quarkcz/watermeter_esp32/src/ikony.h

#pragma once
#include <Arduino.h>
#include <Adafruit_SSD1306.h>

//
// === Deklarace ikon jako bitmap ===
//

// ⚠️ Ikona DANGER 24×24 px
const unsigned char icon_danger24x24[] PROGMEM = {
    0x00,0x00,0x00,  // ........................
    0x00,0x00,0x00,  // ........................
    0x00,0x00,0x00,  // ........................
    0x00,0x18,0x00,  // ...........##...........
    0x00,0x3C,0x00,  // ..........####..........
    0x00,0x7E,0x00,  // .........######.........
    0x00,0x66,0x00,  // .........##..##.........
    0x00,0xE7,0x00,  // ........###..###........
    0x00,0xC3,0x00,  // ........##....##........
    0x01,0x99,0x80,  // .......##..##..##.......
    0x03,0x99,0xC0,  // ......###..##..###......
    0x03,0x18,0xC0,  // ......##...##...##......
    0x07,0x18,0xE0,  // .....###...##...###.....
    0x06,0x18,0x60,  // .....##....##....##.....
    0x0C,0x00,0x30,  // ....##............##....
    0x1C,0x18,0x38,  // ...###.....##.....###...
    0x18,0x18,0x18,  // ...##......##......##...
    0x38,0x00,0x1C,  // ..###..............###..
    0x30,0x00,0x0C,  // ..##................##..
    0x3F,0xFF,0xFC,  // ..####################..
    0x1F,0xFF,0xF8,  // ...##################...
    0x00,0x00,0x00,  // ........................
    0x00,0x00,0x00,  // ........................
    0x00,0x00,0x00   // ........................
};

const unsigned char icon_wifi16x16[] PROGMEM = {
    0x00,0x00,  // ................
    0x07,0xE0,  // .....######.....
    0x1F,0xF8,  // ...##########...
    0x7C,0x3E,  // .#####....#####.
    0xF0,0x0F,  // ####........####
    0xE0,0x03,  // ###...........##
    0x07,0xE0,  // .....######.....
    0x1F,0xF8,  // ...##########...
    0x1C,0x38,  // ...###....###...
    0x18,0x08,  // ...##.......#...
    0x01,0x80,  // .......##.......
    0x03,0xC0,  // ......####......
    0x03,0xC0,  // ......####......
    0x03,0xC0,  // ......####......
    0x01,0x80,  // .......##.......
    0x00,0x00   // ................
};

const unsigned char icon_wifi8x7[] PROGMEM = {
    0x18,  // ...##...
    0x7E,  // .######.
    0xC3,  // ##....##
    0x3C,  // ..####..
    0x66,  // .##..##.
    0x18,  // ...##...
    0x18,  // ...##...
};

const unsigned char icon_wifi_no_signal24x24[] PROGMEM = {
    0x00,0x00,0x00,  // ........................
    0x00,0x00,0x00,  // ........................
    0x00,0x00,0x00,  // ........................
    0x00,0x00,0x00,  // ........................
    0x00,0x78,0x8C,  // .........####...#...##..
    0x03,0xFD,0xDC,  // ......########.###.###..
    0x0F,0xC0,0xF8,  // ....######......#####...
    0x1E,0x00,0x78,  // ...####..........####...
    0x38,0x00,0xF8,  // ..###...........#####...
    0x70,0xFD,0xDC,  // .###....######.###.###..
    0x03,0xF8,0x8C,  // ......#######...#...##..
    0x07,0x80,0x00,  // .....####...............
    0x0E,0x00,0x00,  // ....###.................
    0x00,0x3C,0x00,  // ..........####..........
    0x00,0xFF,0x00,  // ........########........
    0x00,0xE7,0x00,  // ........###..###........
    0x00,0x81,0x00,  // ........#......#........
    0x00,0x18,0x00,  // ...........##...........
    0x00,0x18,0x00,  // ...........##...........
    0x00,0x18,0x00,  // ...........##...........
    0x00,0x00,0x00,  // ........................
    0x00,0x00,0x00,  // ........................
    0x00,0x00,0x00,  // ........................
    0x00,0x00,0x00   // ........................
};

const unsigned char icon_water_drop24x24[] PROGMEM = {
    0x00,0x00,0x00,  // ........................
    0x00,0x18,0x00,  // ...........##...........
    0x00,0x3C,0x00,  // ..........####..........
    0x00,0x7E,0x00,  // .........######.........
    0x00,0xE7,0x00,  // ........###..###........
    0x01,0xC3,0x80,  // .......###....###.......
    0x03,0x81,0xC0,  // ......###......###......
    0x03,0x00,0xC0,  // ......##........##......
    0x07,0x00,0xE0,  // .....###........###.....
    0x06,0x00,0x60,  // .....##..........##.....
    0x0E,0x00,0x70,  // ....###..........###....
    0x0C,0x00,0x30,  // ....##............##....
    0x0C,0x00,0x30,  // ....##............##....
    0x0C,0x01,0xB0,  // ....##.........##.##....
    0x0C,0x01,0xB0,  // ....##.........##.##....
    0x0C,0x03,0xB0,  // ....##........###.##....
    0x0E,0x07,0x70,  // ....###......###.###....
    0x06,0x0E,0x60,  // .....##.....###..##.....
    0x07,0x04,0xE0,  // .....###.....#..###.....
    0x03,0xC3,0xC0,  // ......####....####......
    0x01,0xFF,0x80,  // .......##########.......
    0x00,0x7E,0x00,  // .........######.........
    0x00,0x00,0x00,  // ........................
    0x00,0x00,0x00   // ........................
};

const unsigned char icon_water_drop16x16[] PROGMEM = {
    0x00,0x00,  // ................
    0x01,0x80,  // .......##.......
    0x03,0xC0,  // ......####......
    0x06,0x60,  // .....##..##.....
    0x0C,0x30,  // ....##....##....
    0x08,0x10,  // ....#......#....
    0x18,0x18,  // ...##......##...
    0x10,0x08,  // ...#........#...
    0x10,0x28,  // ...#......#.#...
    0x10,0x28,  // ...#......#.#...
    0x10,0x68,  // ...#.....##.#...
    0x18,0xD8,  // ...##...##.##...
    0x0C,0x30,  // ....##....##....
    0x07,0xE0,  // .....######.....
    0x01,0x80,  // .......##.......
    0x00,0x00   // ................
};

const unsigned char icon_lock_1_8x7[] PROGMEM = {
    0x18,  // ...##...
    0x3C,  // ..####..
    0x24,  // ..#..#..
    0x7E,  // .######.
    0x42,  // .#....#.
    0x42,  // .#....#.
    0x7E   // .######.
};

const unsigned char icon_lock_2_8x7[] PROGMEM = {
    0x18,  // ...##...
    0x24,  // ..#..#..
    0x24,  // ..#..#..
    0x7E,  // .######.
    0x7E,  // .######.
    0x7E,  // .######.
    0x7E   // .######.
};

const unsigned char icon_four_dots_narrow16x5[] PROGMEM = {
    0x00,0x00,  // ................
    0x44,0x44,  // .#...#...#...#..
    0xAA,0xAA,  // #.#.#.#.#.#.#.#.
    0x44,0x44,  // .#...#...#...#..
    0x00,0x00   // ................
};

const unsigned char icon_wifi_cover24x24[] PROGMEM = {
    0xFF,0xFF,0xFF,  // ########################
    0xFF,0xFF,0xFF,  // ########################
    0xC0,0x00,0x03,  // ##....................##
    0xC0,0x00,0x03,  // ##....................##
    0xC0,0x00,0x03,  // ##....................##
    0xC0,0x00,0x03,  // ##....................##
    0xC0,0x7E,0x03,  // ##.......######.......##
    0xC1,0xFF,0xC3,  // ##.....###########....##
    0xC7,0xFF,0xE3,  // ##...##############...##
    0xCF,0x00,0xF3,  // ##..####........####..##
    0xCC,0x00,0x33,  // ##..##............##..##
    0xC0,0x7E,0x03,  // ##.......######.......##
    0xC1,0xFF,0x83,  // ##.....##########.....##
    0xC3,0xE7,0xC3,  // ##....#####..#####....##
    0xC3,0x00,0xC3,  // ##....##........##....##
    0xC0,0x00,0x03,  // ##....................##
    0xC0,0x18,0x03,  // ##.........##.........##
    0xC0,0x18,0x03,  // ##.........##.........##
    0xC0,0x00,0x03,  // ##....................##
    0xC0,0x00,0x03,  // ##....................##
    0xC0,0x00,0x03,  // ##....................##
    0xC0,0x00,0x03,  // ##....................##
    0xFF,0xFF,0xFF,  // ########################
    0xFF,0xFF,0xFF   // ########################
};

// 🧩 Datová struktura pro ikonu
struct IconDef {
    const char* name;
    const unsigned char* bitmap;
    uint8_t width;
    uint8_t height;
};

// 🧠 Seznam všech ikon
const IconDef iconList[] = {
    { "danger24x24", icon_danger24x24, 24, 24 },
    { "wifi16x16", icon_wifi16x16, 16, 16 },
    { "wifi8x7", icon_wifi8x7, 8, 8 },
    { "wifi_cover24x24", icon_wifi_cover24x24, 24, 24 },
    { "wifi_no_signal24x24", icon_wifi_no_signal24x24, 24, 24 },
    { "four_dots_narrow16x5", icon_four_dots_narrow16x5, 16, 5 },
    { "lock_1", icon_lock_1_8x7, 8, 7 },
    { "lock_2", icon_lock_2_8x7, 8, 7 },
    { "water_drop24x24", icon_water_drop24x24, 24, 24 },
    { "water_drop16x16", icon_water_drop16x16, 16, 16 },
};

const uint8_t ICON_COUNT = sizeof(iconList) / sizeof(iconList[0]);

//
// === Funkce pro vykreslení ikony ===
//
void DrawIcon(Adafruit_SSD1306 &display, const char* name, int16_t x, int16_t y) {
    for (uint8_t i = 0; i < ICON_COUNT; i++) {
        if (strcmp(iconList[i].name, name) == 0) {
            display.drawBitmap(x, y, iconList[i].bitmap, iconList[i].width, iconList[i].height, SSD1306_WHITE);
            return;
        }
    }

    // Pokud ikona nenalezena
    display.setTextSize(1);
    display.setTextColor(SSD1306_WHITE);
    display.setCursor(x, y);
    display.print("?");
}
